Plaenkler/Gulu_ESP32-C3_ePaper/Gulu_ESP32-C3_ePaper_3D/52435-2471.stp

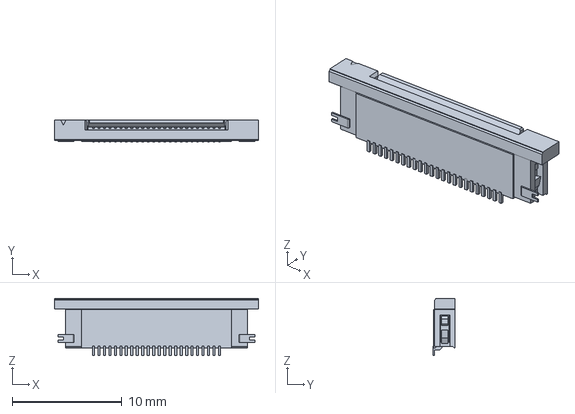
[picture p15: CAD file, 2024-02-22]
Gulu_ESP32-C3_ePaper_3D/52435-2471.stp
18.6 x 2.05 x 5.20 mm
